Iverson-45/Vehicle-movement-parameters/Main MCU/Inc/main.h

#ifndef MAIN_H_
#define MAIN_H_

#include <stdint.h>
#include <math.h>
#include <stdio.h>
#include <string.h>
#include <stdlib.h>

#include "stm32f4xx.h"
#include "gpio.h"
#include "SysTick.h"
#include "uart.h"
#include "gps.h"
#include "i2c.h"
#include "bmi160.h"
#include "clock.h"



#endif
