Iverson-45/Vehicle-movement-parameters/LCD MCU/Src/gpio.c

#include "gpio.h"

void MX_GPIO_Init(void)
{
  GPIO_InitTypeDef GPIO_InitStruct = {0};

  /* GPIO Ports Clock Enable */
  __HAL_RCC_GPIOF_CLK_ENABLE();
  __HAL_RCC_GPIOA_CLK_ENABLE();
  __HAL_RCC_GPIOB_CLK_ENABLE();

  /*Configure GPIO pin Output Level */
  HAL_GPIO_WritePin(GPIOA, TFT_CS_Pin|TFT_DC_Pin|TFT_RST_Pin, GPIO_PIN_RESET);

  /* SD_CS High (Deselect) */
  HAL_GPIO_WritePin(SD_CS_GPIO_Port, SD_CS_Pin, GPIO_PIN_SET);

  /*Configure GPIO pin : ENC_BTN_Pin */
  GPIO_InitStruct.Pin = ENC_BTN_Pin;
  GPIO_InitStruct.Mode = GPIO_MODE_INPUT;
  GPIO_InitStruct.Pull = GPIO_PULLUP;
  HAL_GPIO_Init(ENC_BTN_GPIO_Port, &GPIO_InitStruct);

  /*Configure GPIO pin : TFT_CS_Pin */
  GPIO_InitStruct.Pin = TFT_CS_Pin;
  GPIO_InitStruct.Mode = GPIO_MODE_OUTPUT_PP;
  GPIO_InitStruct.Pull = GPIO_NOPULL;
  GPIO_InitStruct.Speed = GPIO_SPEED_FREQ_HIGH;
  HAL_GPIO_Init(TFT_CS_GPIO_Port, &GPIO_InitStruct);

  /*Configure GPIO pins : TFT_DC_Pin TFT_RST_Pin */
  GPIO_InitStruct.Pin = TFT_DC_Pin|TFT_RST_Pin;
  GPIO_InitStruct.Mode = GPIO_MODE_OUTPUT_PP;
  GPIO_InitStruct.Pull = GPIO_NOPULL;
  GPIO_InitStruct.Speed = GPIO_SPEED_FREQ_LOW;
  HAL_GPIO_Init(GPIOA, &GPIO_InitStruct);

  /*Configure GPIO pin : SD_CS_Pin */
  GPIO_InitStruct.Pin = SD_CS_Pin;
  GPIO_InitStruct.Mode = GPIO_MODE_OUTPUT_PP;
  GPIO_InitStruct.Pull = GPIO_NOPULL;
  GPIO_InitStruct.Speed = GPIO_SPEED_FREQ_HIGH;
  HAL_GPIO_Init(SD_CS_GPIO_Port, &GPIO_InitStruct);

  /* ZMIANA: SD_DETECT jako PRZERWANIE (Obocze narastające i opadające)
     Pin: PB1 -> EXTI1
  */
  GPIO_InitStruct.Pin = SD_DETECT_Pin;
  GPIO_InitStruct.Mode = GPIO_MODE_IT_RISING_FALLING;
  GPIO_InitStruct.Pull = GPIO_PULLUP;
  HAL_GPIO_Init(SD_DETECT_GPIO_Port, &GPIO_InitStruct);

  /* Włączamy przerwanie w NVIC */
  HAL_NVIC_SetPriority(EXTI1_IRQn, 0, 0);
  HAL_NVIC_EnableIRQ(EXTI1_IRQn);
}
